Vin-doong/smartfishbowl/3D프린터관련/LCD케이스.JPG

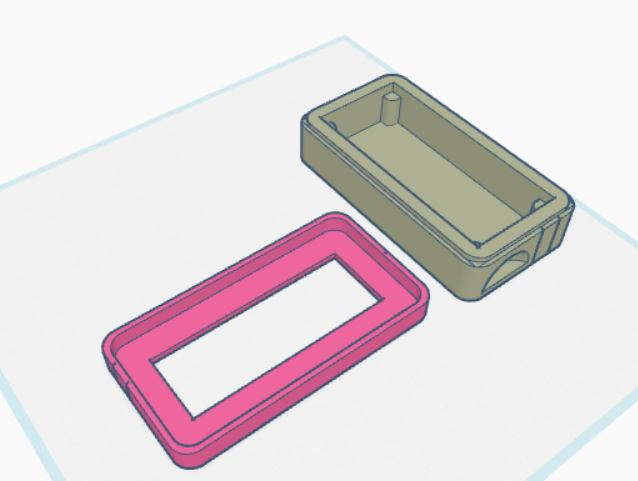
3D프린터관련/LCD케이스.JPG
