Vin-doong/smartfishbowl/3D프린터관련/LED거치대.JPG

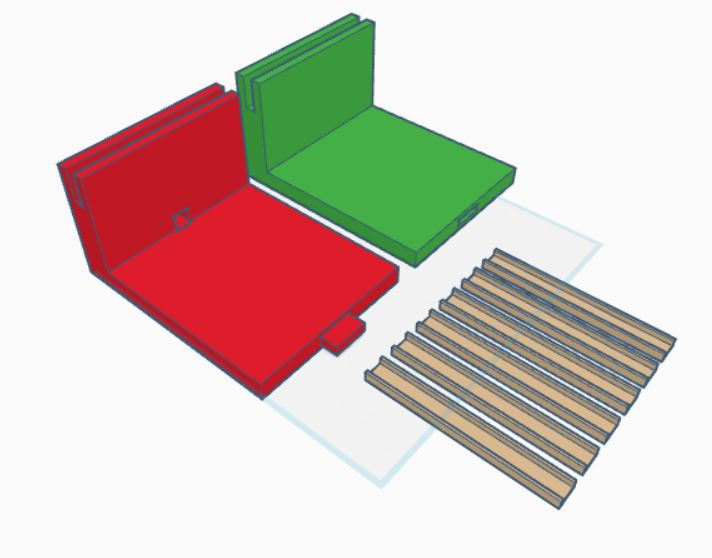
3D프린터관련/LED거치대.JPG
