Vin-doong/smartfishbowl/3D프린터관련/기타출력물.JPG

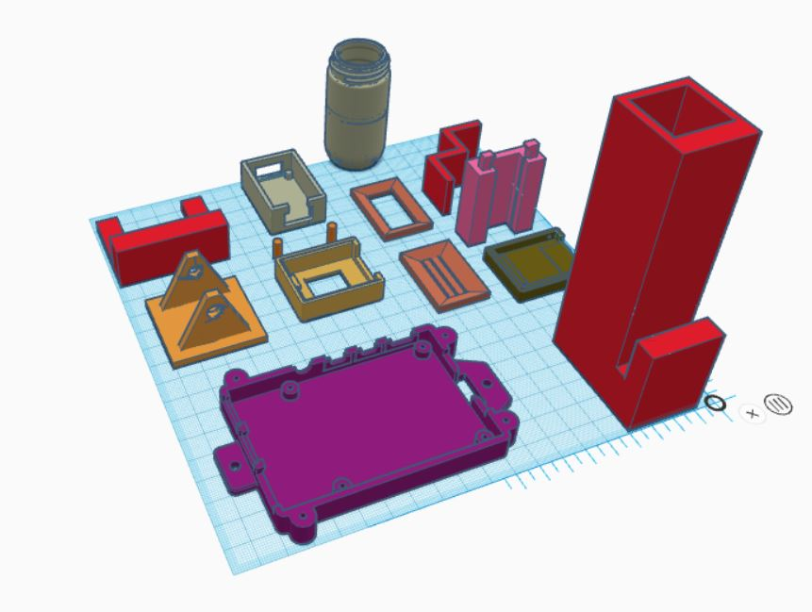
3D프린터관련/기타출력물.JPG
