Vin-doong/smartfishbowl/3D프린터관련/먹이공급기.JPG

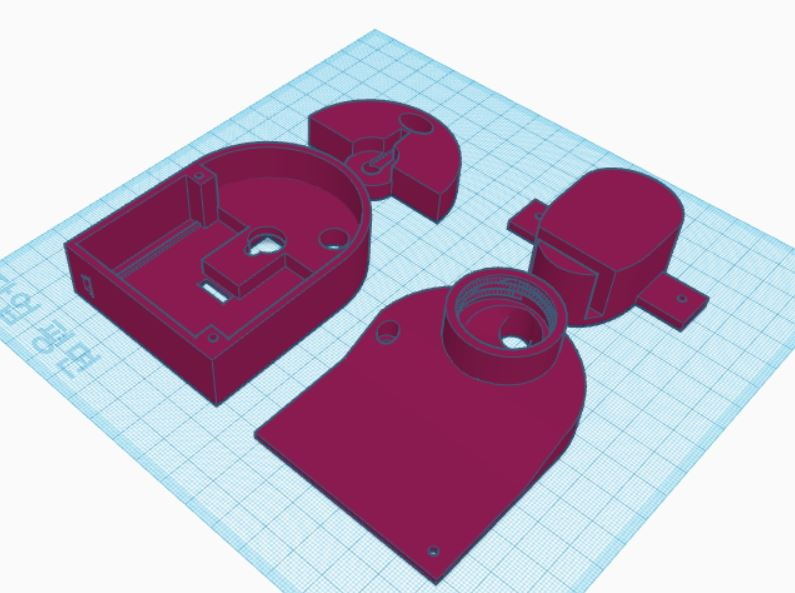
3D프린터관련/먹이공급기.JPG
