Vin-doong/smartfishbowl/3D프린터관련/물순환프로펠러.JPG

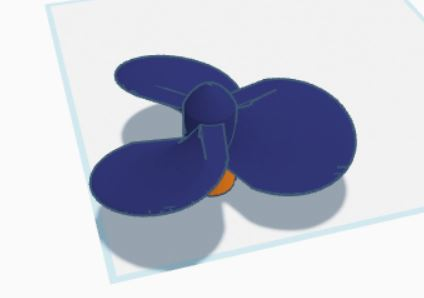
3D프린터관련/물순환프로펠러.JPG
