Vin-doong/smartfishbowl/3D프린터관련/컨트롤박스.JPG

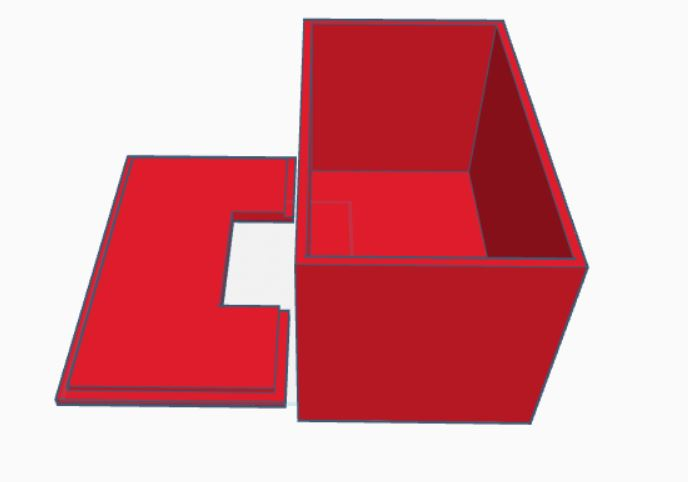
3D프린터관련/컨트롤박스.JPG
