Vin-doong/smartfishbowl/3D프린터관련/파이카메라거치대.JPG

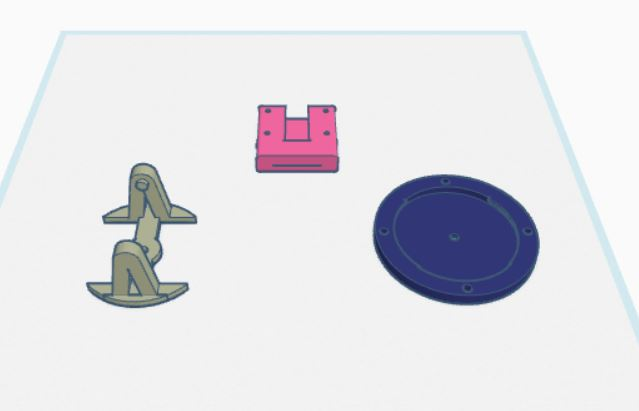
3D프린터관련/파이카메라거치대.JPG
