Vin-doong/smartfishbowl/기타자료/스마트어항_알고리즘.png

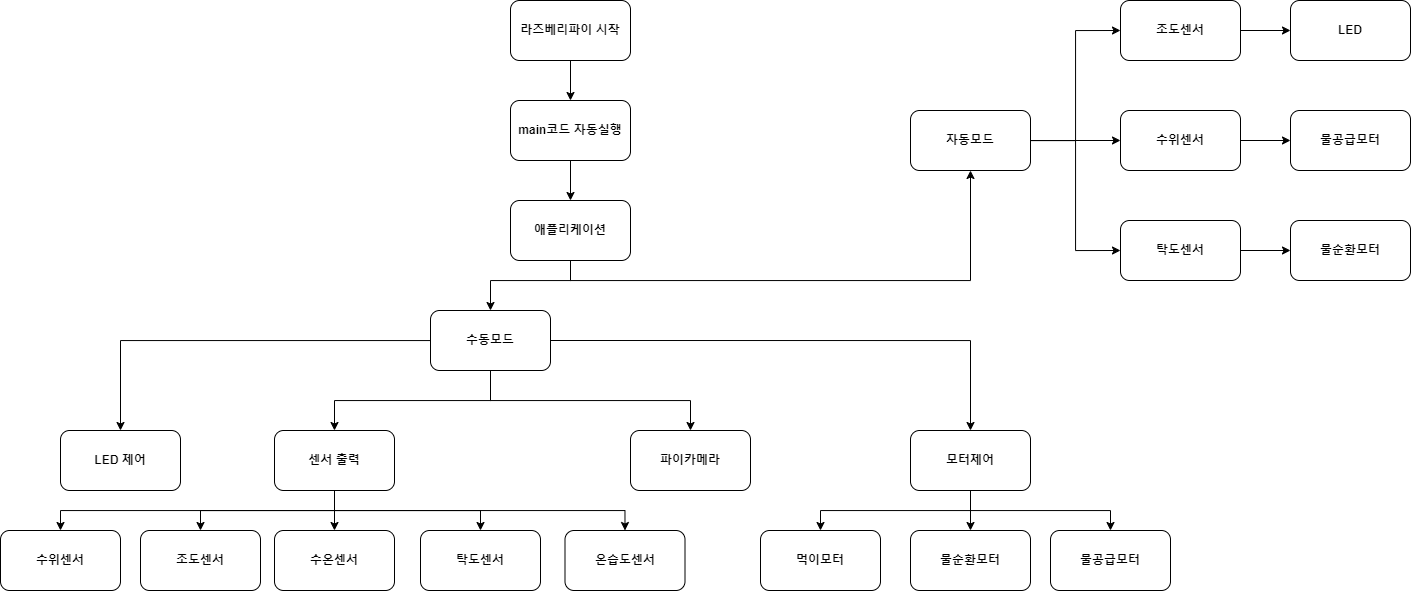
기타자료/스마트어항_알고리즘.png
