Vin-doong/smartfishbowl/앱제작파일/블록도/스마트어항자동모드.JPG

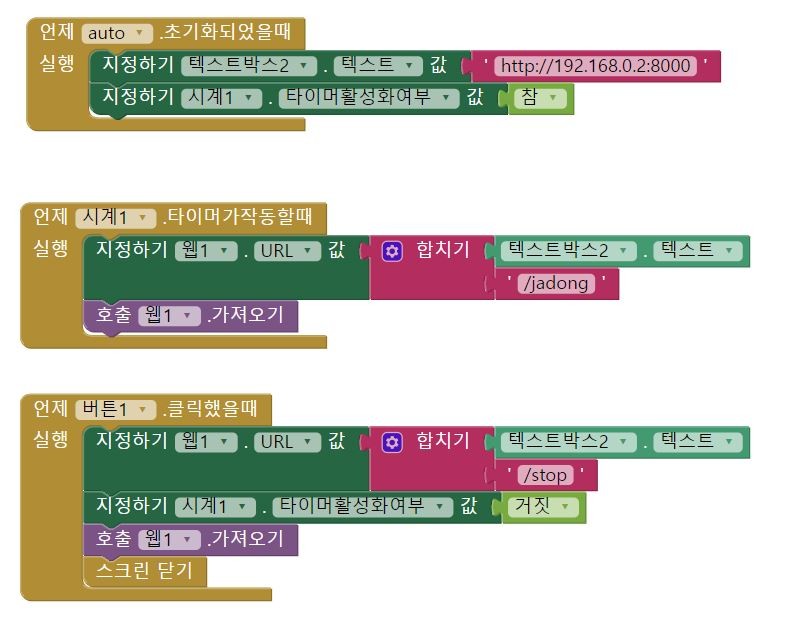
앱제작파일/블록도/스마트어항자동모드.JPG
