Vin-doong/smartfishbowl/앱제작파일/아이콘/fish-food.png

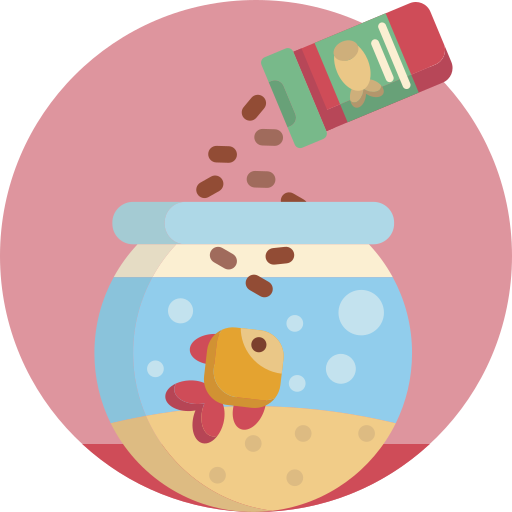
앱제작파일/아이콘/fish-food.png
