Vin-doong/smartfishbowl/앱제작파일/아이콘/sea-level.png

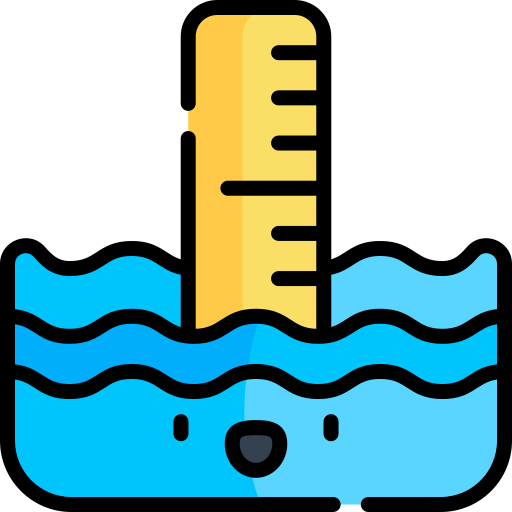
앱제작파일/아이콘/sea-level.png
