Vin-doong/smartfishbowl/앱제작파일/아이콘/thermometer.png

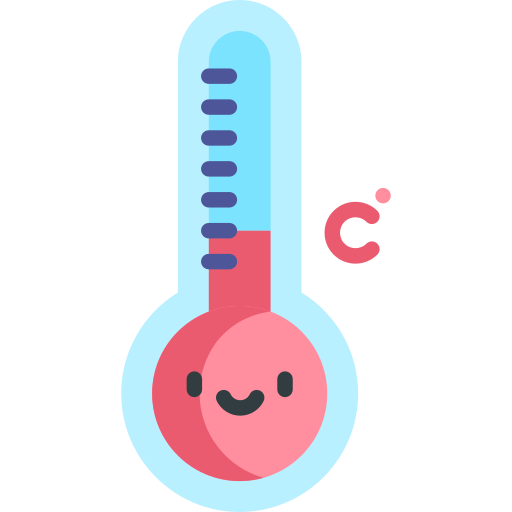
앱제작파일/아이콘/thermometer.png
