Vin-doong/smartfishbowl/앱제작파일/아이콘/water-pollution.png

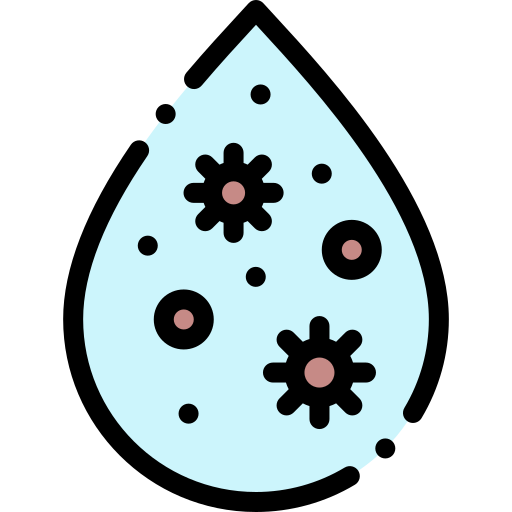
앱제작파일/아이콘/water-pollution.png
