Vin-doong/smartfishbowl/회로도/스마트어항최종회로.JPG

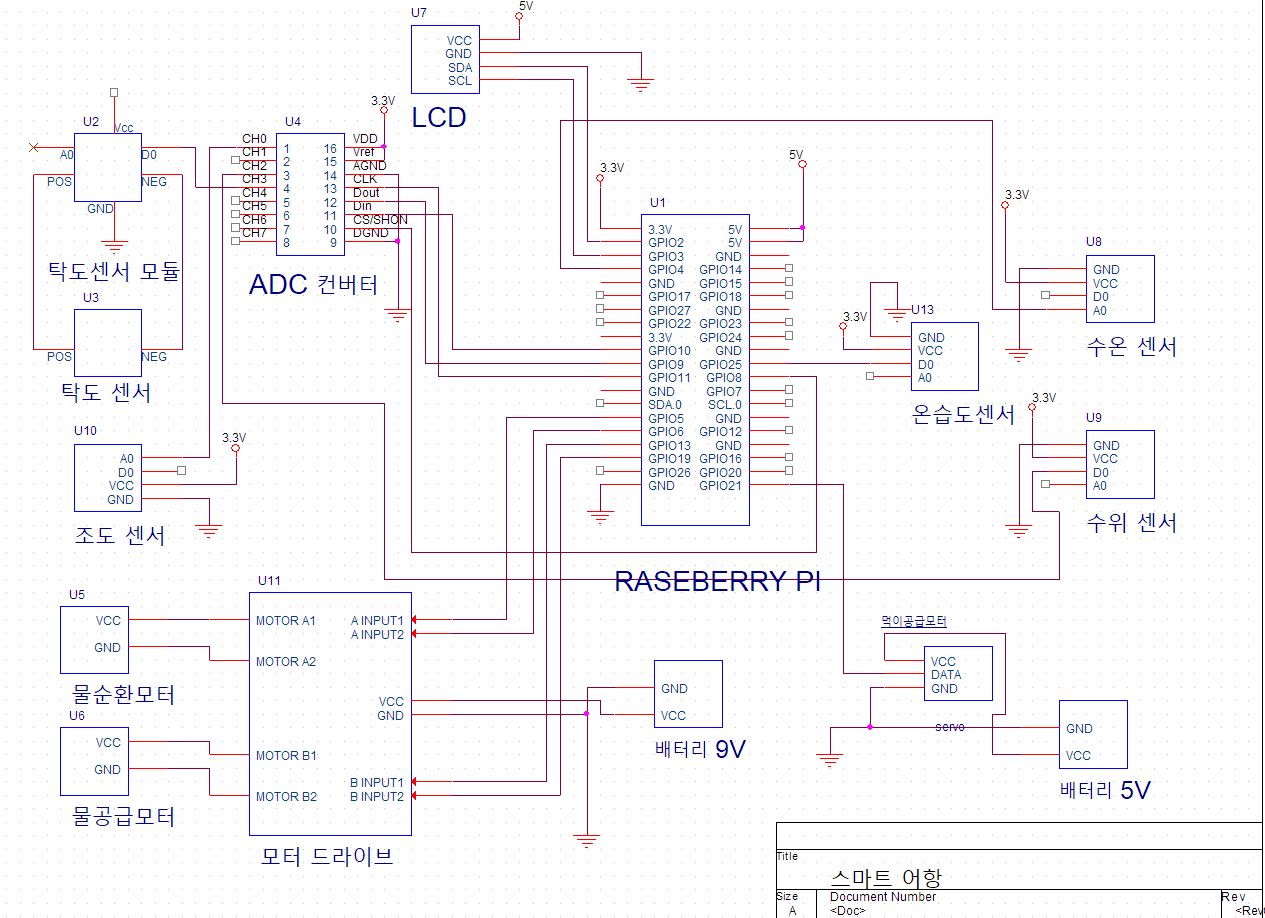
회로도/스마트어항최종회로.JPG
