Vin-doong/smartfishbowl/회로도/학기초구상회로도.PNG

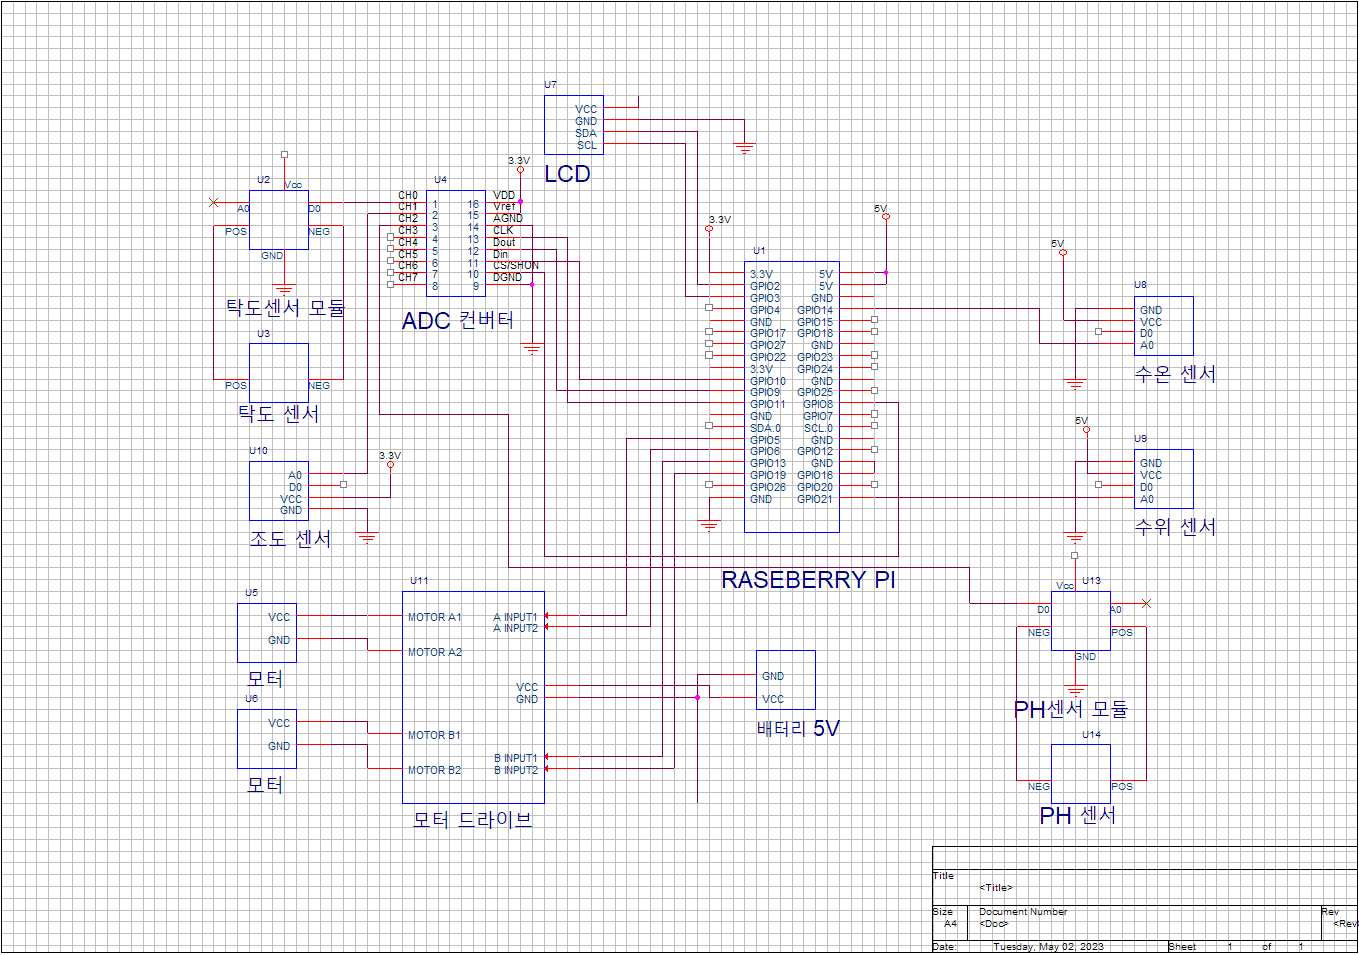
회로도/학기초구상회로도.PNG
