Vin-doong/smartfishbowl/코딩파일/이전코드(최종이전의파일)/테스트용코드/ph.py

#!/usr/bin/python3 

import Adafruit_DHT      # 라이브러리 불러오기
import RPi.GPIO as GPIO
import smbus

sensor = Adafruit_DHT.DHT11     #  sensor 객체 생성

pin = 18                     # Data핀의 GPIO핀 넘버

humidity, temperature = Adafruit_DHT.read_retry(sensor, pin)   # 센서 객체에서 센서 값(ㅇ노도, 습도) 읽기

      
if humidity is not None and temperature is not None:   #습도 및 온도 값이 모두 제대로 읽혔다면 
    print('Temp={0:0.1f}*C  Humidity={1:0.1f}%'.format(temperature, humidity))  # 온도, 습도 순으로 표시
else:                                                  # 에러가 생겼다면 
    print('Failed to get reading. Try again!')        #  에러 표시
