Vin-doong/smartfishbowl/코딩파일/이전코드(최종이전의파일)/테스트용코드/takdo.py

import RPi.GPIO as GPIO
import time

GPIO.setmode(GPIO.BCM)

GPIO.setup(18, GPIO.IN, pull_up_down = GPIO.PUD_UP)

while True:
	input_state = GPIO.input(18)
	if input_state == False:
		print('sensor blocked')
		time.sleep(0.2)
