Vin-doong/smartfishbowl/코딩파일/이전코드(최종이전의파일)/테스트용코드/test2.py

import cv2
from picamera2 import Picamera2
piCam=Picamera2()
piCam.preview_configuration.main.size=(1280,720)
piCam.preview_configuration.main.format="RGB888"
piCam.preview_configuration.align()
piCam.configure("preview")
piCam.start()
while True:
    frame=piCam.capture_array()
    cv2.imshow("piCam",frame)
    if cv2.waitKey(1)==ord('q'):
        break
cv2.destroyAllwindows()
